Gtrx0/lysergic25/MX_Alps_Hybrid.pretty-master/Screenshots/Render-Bottomside.png

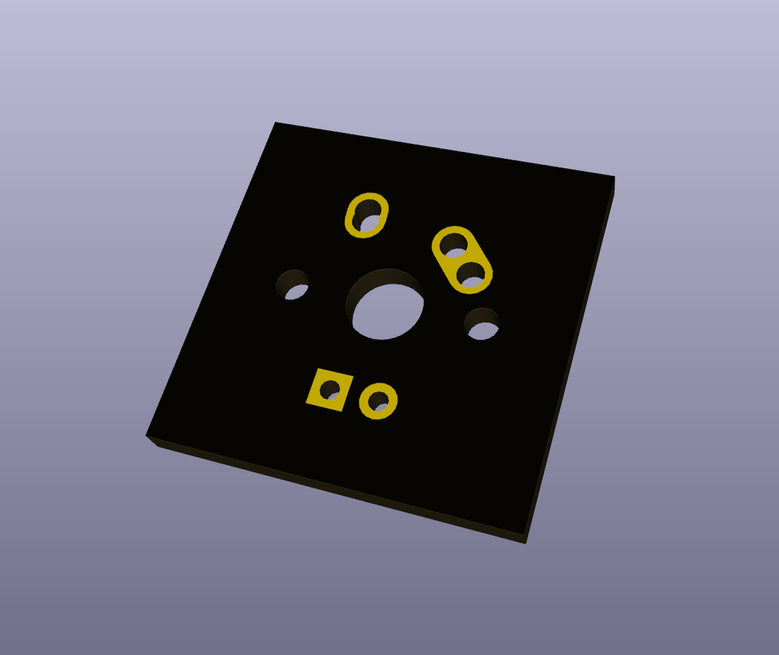
MX_Alps_Hybrid.pretty-master/Screenshots/Render-Bottomside.png
