Gtrx0/lysergic25/MX_Alps_Hybrid.pretty-master/Screenshots/Schematic.png

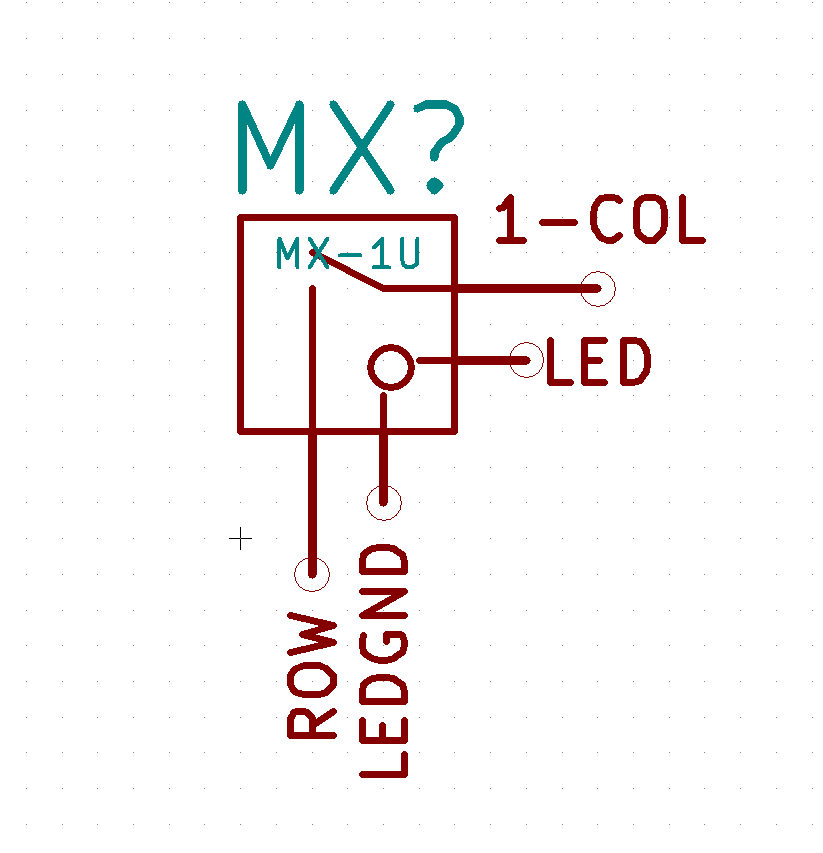
MX_Alps_Hybrid.pretty-master/Screenshots/Schematic.png
