Gtrx0/lysergic25/Take_Acid/GitHub-Mark-Light-120px-plus.png

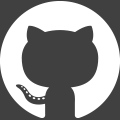
Take_Acid/GitHub-Mark-Light-120px-plus.png
