Gtrx0/lysergic25/Take_Acid/LysergicMolecule.bmp

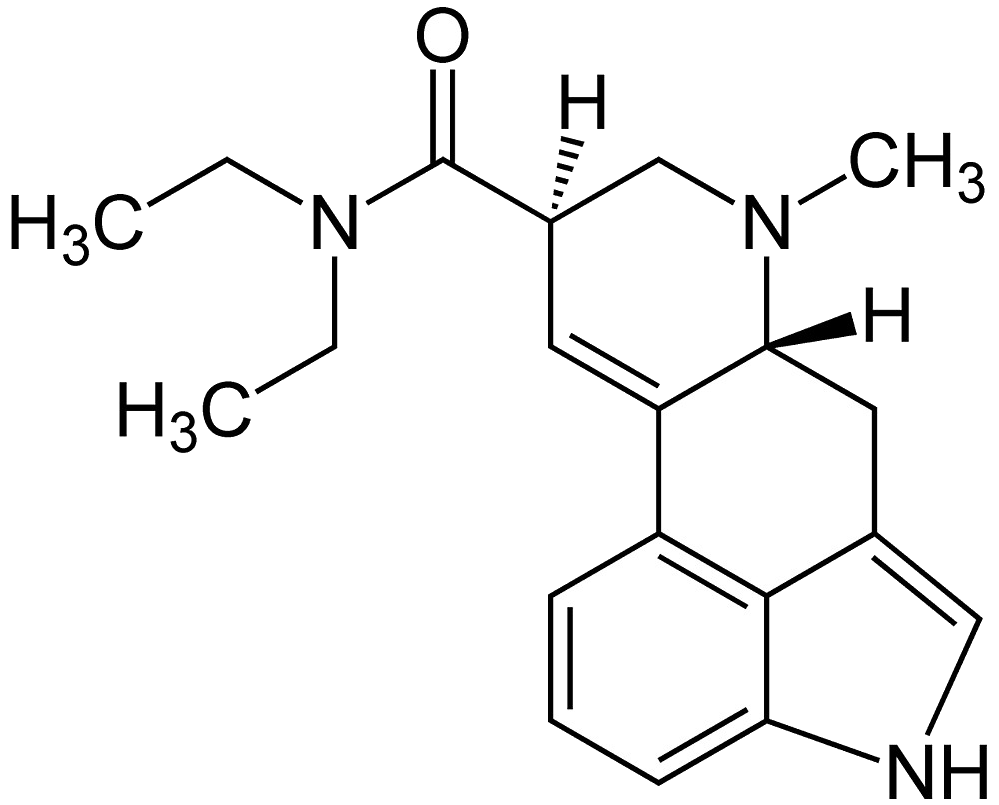
Take_Acid/LysergicMolecule.bmp
