Gtrx0/lysergic25/Take_Acid/TAKEACID_head.bmp

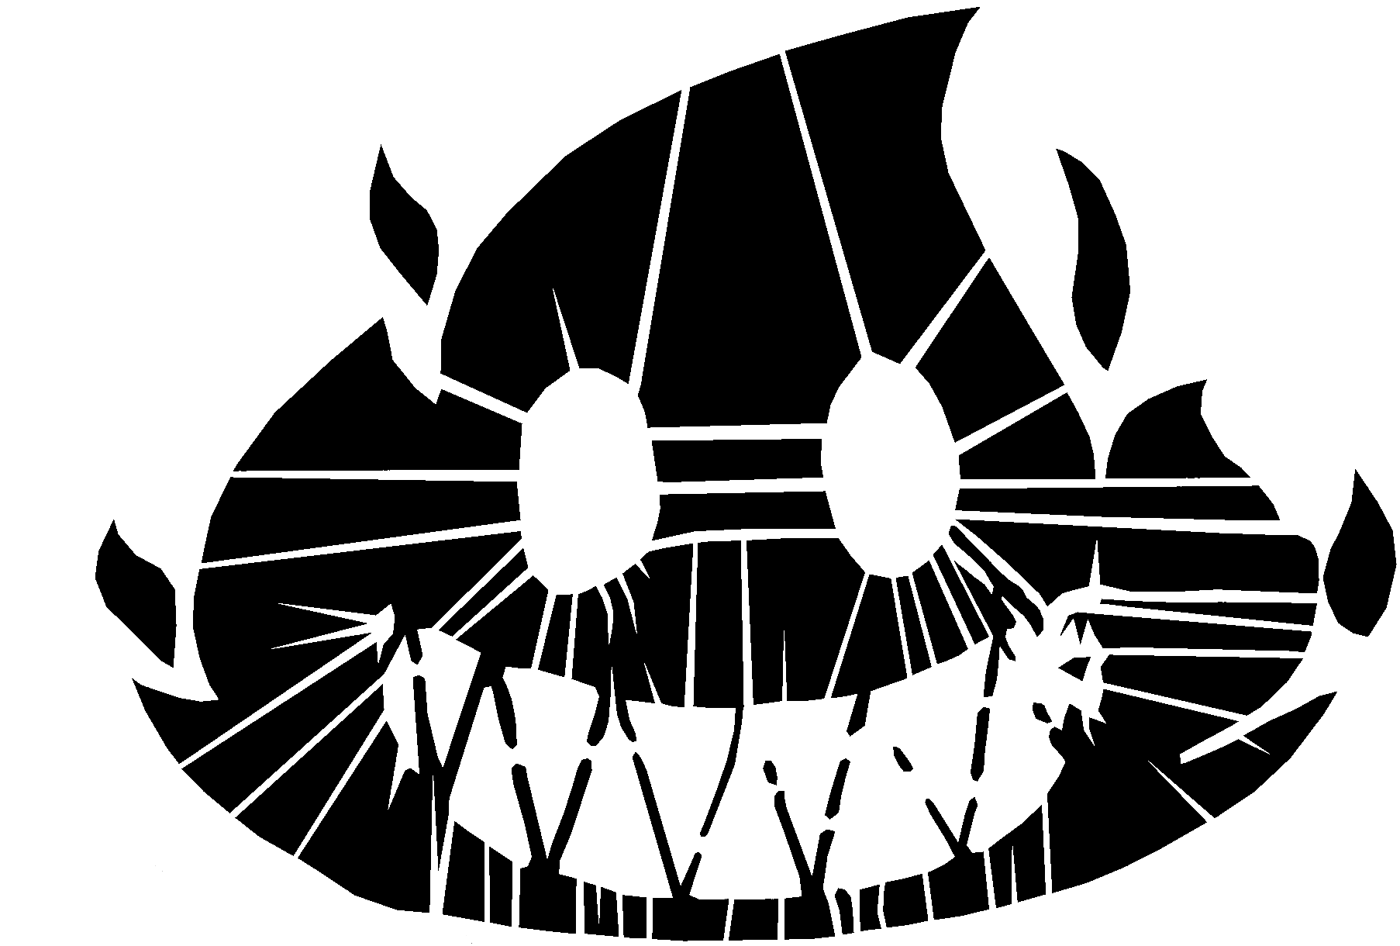
Take_Acid/TAKEACID_head.bmp
