Gtrx0/lysergic25/Take_Acid/Sticker material-PNG.png

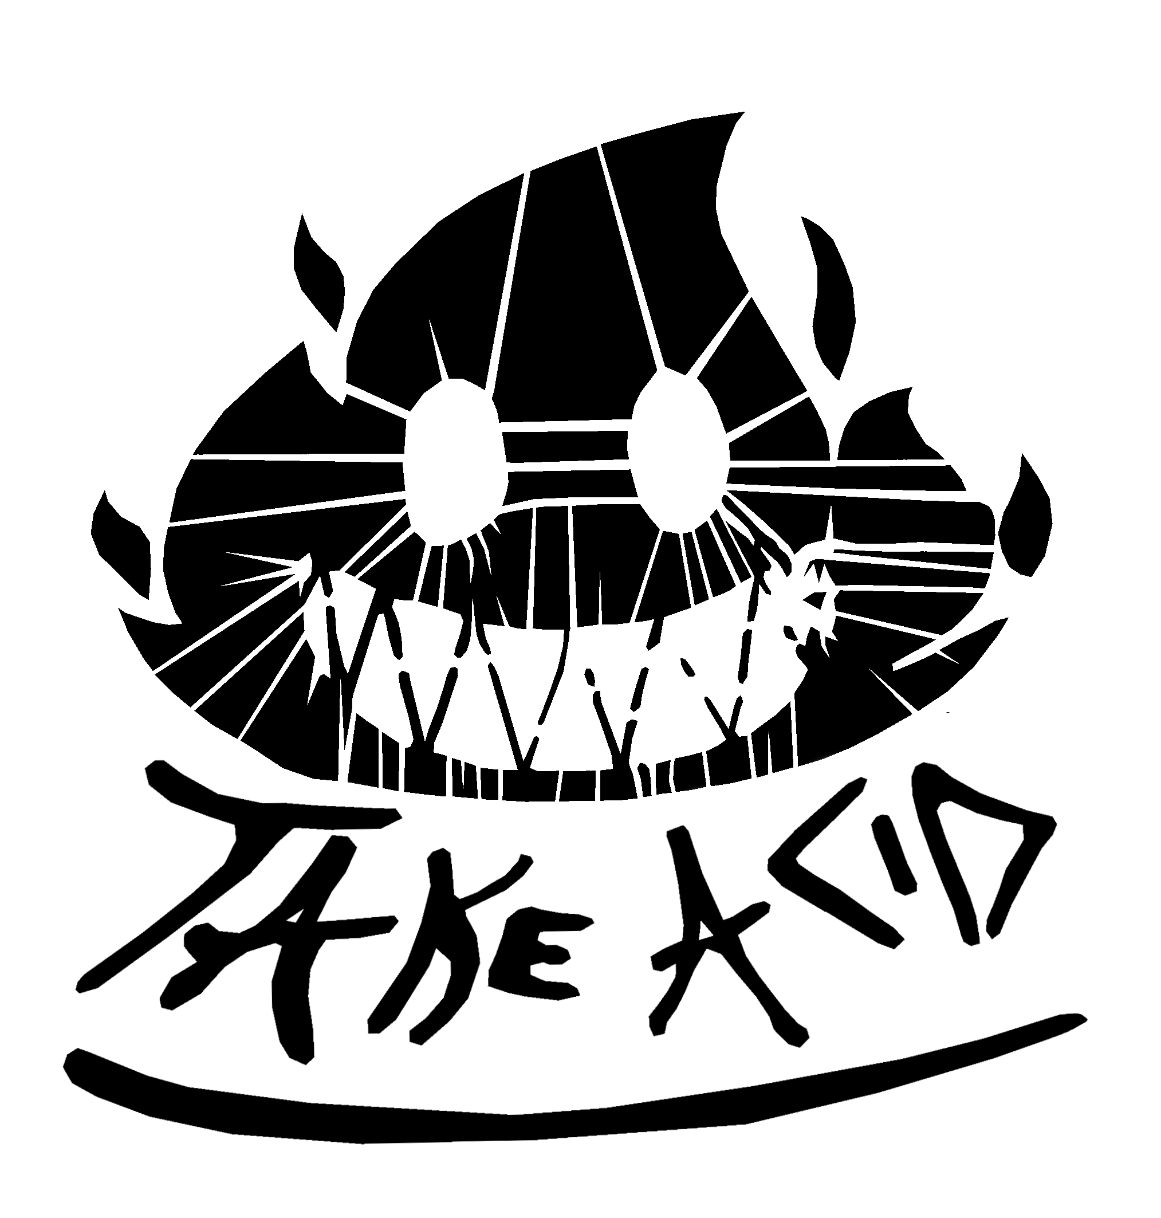
Take_Acid/Sticker material-PNG.png
