Gtrx0/lysergic25/3D/WS2812_RGB_LED_updated.stp

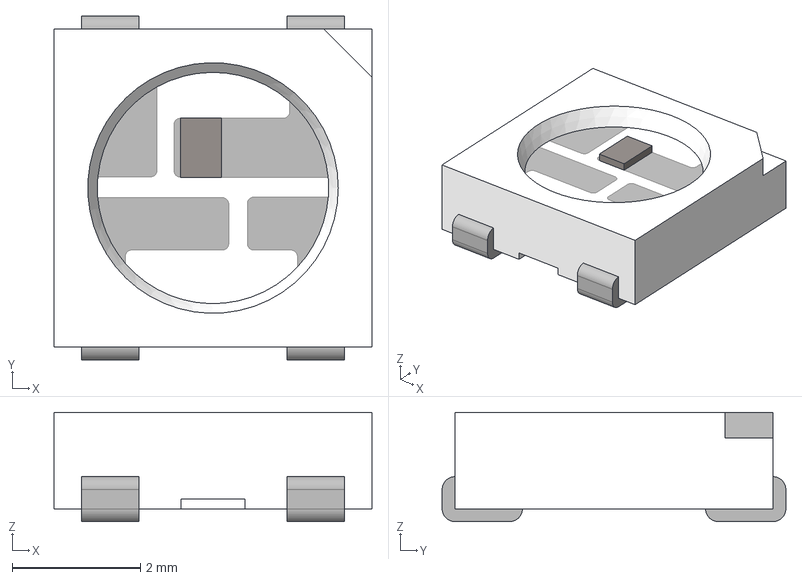
[picture p29: CAD file, 2018-08-20]
3D/WS2812_RGB_LED_updated.stp
4.95 x 5.35 x 1.70 mm
