Gtrx0/lysergic25/3D/res1206r.STEP

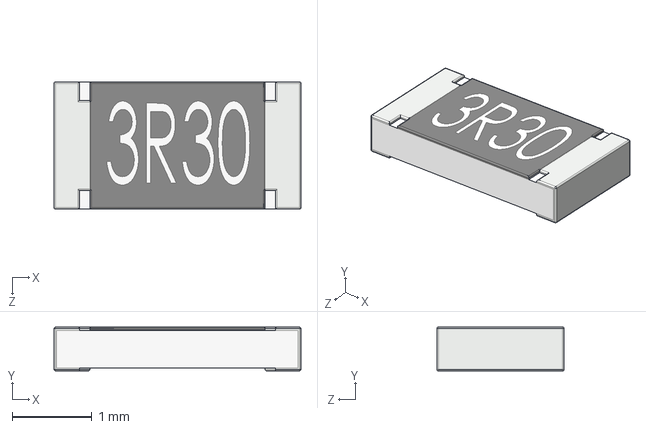
[picture p30: CAD file, 2018-08-20]
3D/res1206r.STEP
3.10 x 0.551 x 1.60 mm
