Gtrx0/lysergic25/3D/TO-253AA.stp

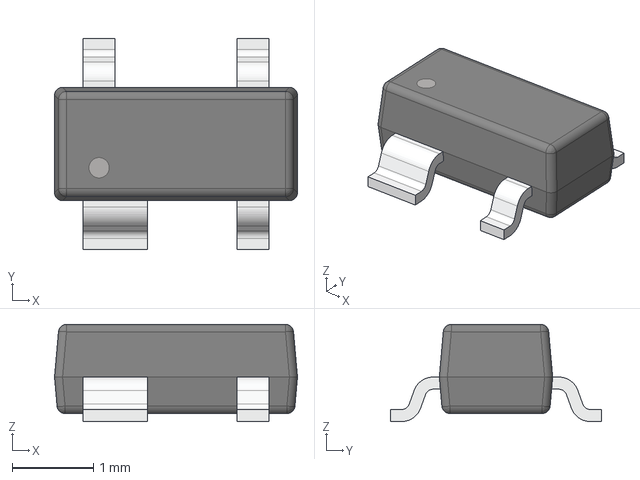
[picture p31: CAD file, 2018-08-20]
3D/TO-253AA.stp
3.00 x 2.60 x 1.20 mm
