Gtrx0/lysergic25/Nexperia/Nexperia/3D/SOT402 MO153 TSSOP14-1_orig.step

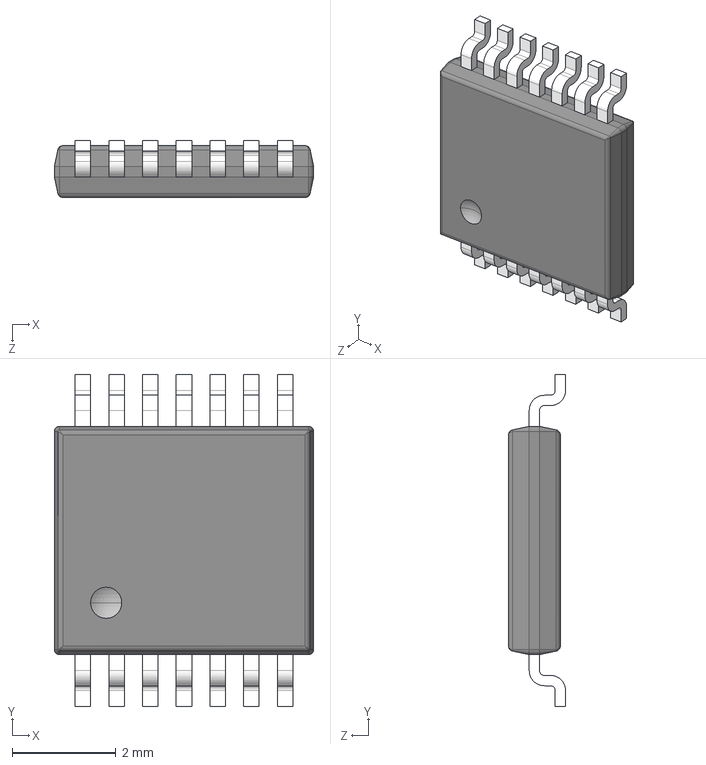
[picture p32: CAD file, 2018-08-20]
Nexperia/Nexperia/3D/SOT402 MO153 TSSOP14-1_orig.step
5.00 x 6.40 x 1.10 mm
